ACloakedFly/Thoths-Oracle/Images/20250720_190244.JPG

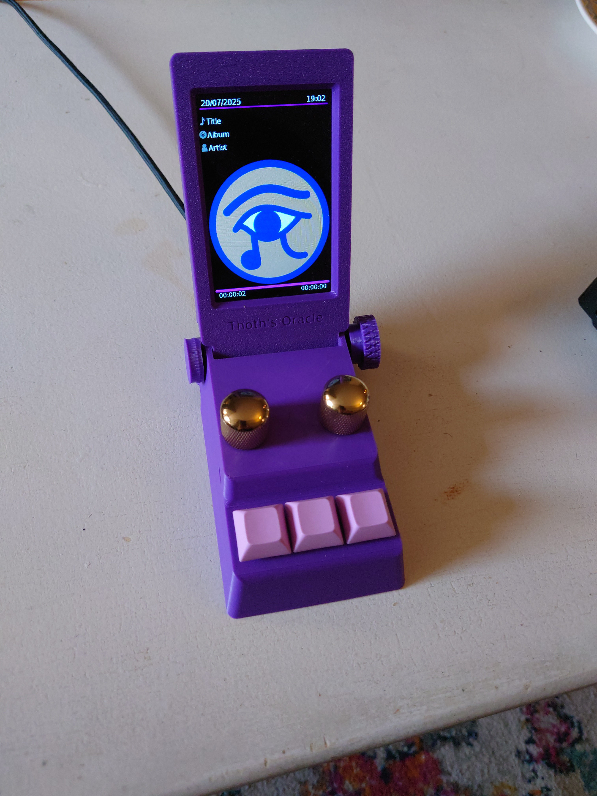
Images/20250720_190244.JPG
