ACloakedFly/Thoths-Oracle/Images/Assembly_Pics/20250726_150619.JPG

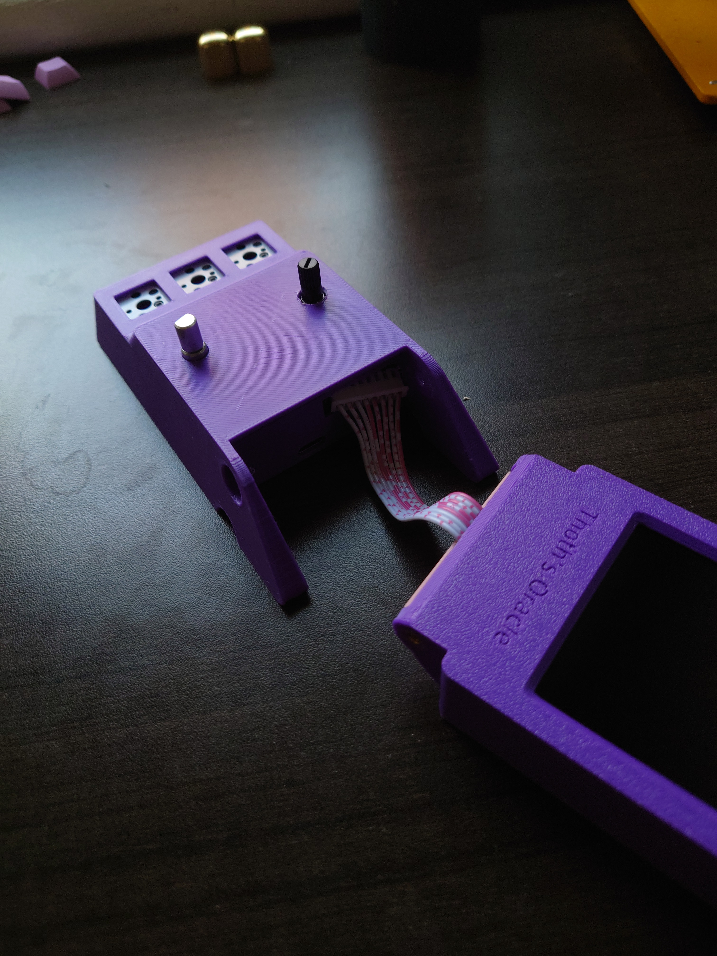
Images/Assembly_Pics/20250726_150619.JPG
