ACloakedFly/Thoths-Oracle/Images/Assembly_Pics/20250726_150648.JPG

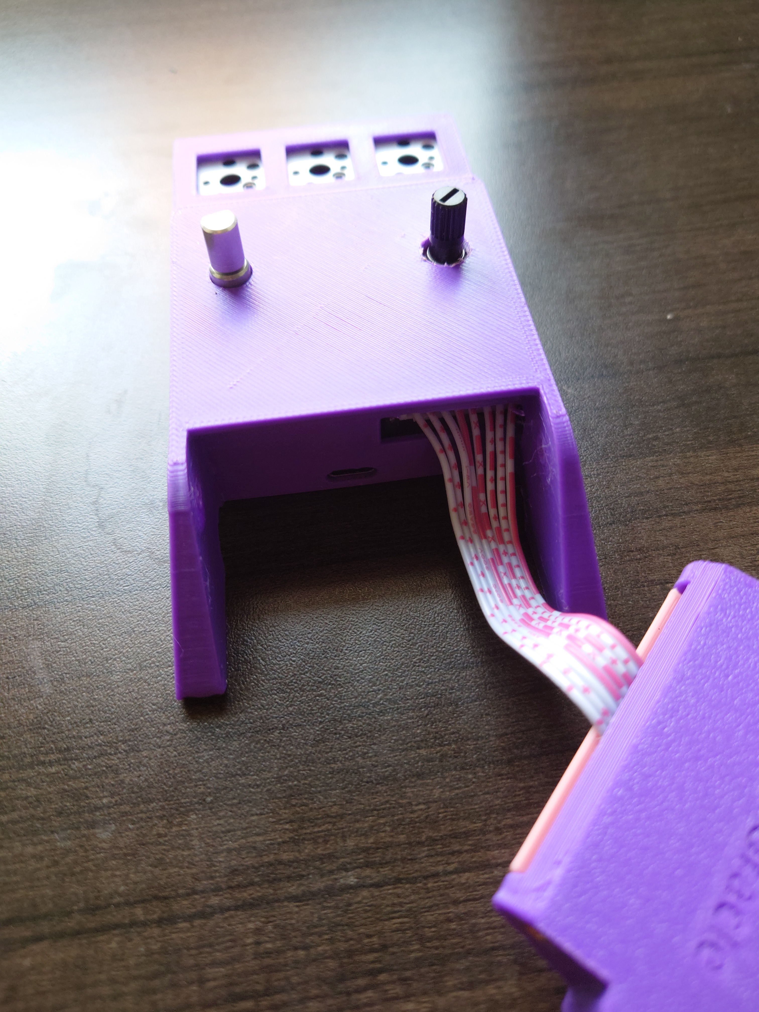
Images/Assembly_Pics/20250726_150648.JPG
