ACloakedFly/Thoths-Oracle/Firmware/main/data.h

/*
===========================================================================
Copyright (C) 2025 Dominique Negm

This file is part of Thoth's Oracle source code.

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
You should have received a copy of the GNU General Public License
along with Thoth's Oracle; if not, see <https://www.gnu.org/licenses/>
===========================================================================
*/
// data.h

#include <string.h>
#include <stdio.h>
#include <stddef.h>
#include <stdlib.h>
#include <stdint.h>
#include <wchar.h>
#include <time.h>
#include "freertos/FreeRTOS.h"
#include "freertos/semphr.h"
#include "freertos/task.h"
#include "freertos/queue.h"
#include "esp_err.h"
#include "esp_log.h"
#include "esp_timer.h"
#include "esp_lcd_panel_io.h"
#include "esp_lcd_panel_vendor.h"
#include "esp_lcd_panel_ops.h"
#include "driver/gpio.h"
#include "driver/spi_master.h"
#include "driver/usb_serial_jtag.h"
#include "driver/ledc.h"
#include "lvgl.h"
#include "button_gpio.h"
#include "iot_button.h"
#include "esp_sleep.h"
#include "driver/pulse_cnt.h"
#include "esp_lcd_ili9341.h"
#include "esp_task_wdt.h"

#define UTF8 1
#define UTF16 2
#define UTF32 4
#define BITS UTF8
#define CHARS 100
#define HEADER_BYTES 12

#define portDelay 50
#define RX_BUF_SIZE (1024)
#define TX_BUF_SIZE (512)

//Inputs
#define PREV_PIN        7
#define MUTE_PIN        2
#define PLAY_PIN        8
#define NEXT_PIN        6
#define ENC_EDGE_PIN    4
#define ENC_LEVEL_PIN   5

//Inputs commands
#define CMD_VAL_VOL_DN      1
#define CMD_VAL_VOL_UP      2
#define CMD_VAL_MUTE        3
#define CMD_VAL_PREV        4
#define CMD_VAL_PLAY_PAUSE  5
#define CMD_VAL_NEXT        6

//Message types
#define IMG_TAG         1
#define TEXT_TAG        2
#define SYS_MSG_TAG     3
#define DUR_POS_TAG     4
#define CMD_TAG         5
#define INFO_TAG        6
#define STATUS_TAG      7
#define FINISHED_TAG    8
#define ERROR_TAG       9
#define COLOUR_TAG      10

//Display
#define PIN_NUM_SCLK        11
#define PIN_NUM_MOSI        10
#define PIN_NUM_LCD_DC      9
#define PIN_NUM_LCD_RST     12
#define PIN_NUM_LCD_CS      13
#define PIN_NUM_MISO        -1//Unused

//Image
#define IMG_WIDTH   304
#define IMG_HEIGHT  304
#define IMG_SIZE IMG_HEIGHT*IMG_WIDTH*2//Images are in RGB565 format so every pixel needs 2 bytes

//Text, added multiple opions to allow for faster testing, can ignore this section
#define TEXT_SIZE 512
#if BITS == 1
#define CHAR_SIZE uint8_t
#define CHAR_TYPE unsigned char
#define char_cpy memcpy
#elif BITS == 2
#define CHAR_SIZE uint16_t
#define CHAR_TYPE wchar_t
#define char_cpy wmemcpy
#else
#define CHAR_SIZE uint32_t
#define CHAR_TYPE wchar_t
#define char_cpy wmemcpy
#endif

#define DUR_POS_BYTES 8
extern const char TAG[3];
extern char name[TEXT_SIZE];
extern bool updated;
extern uint8_t album_cover[IMG_SIZE + RX_BUF_SIZE];//Added an extra buffer at the end just incase
extern uint8_t width, height;
extern uint32_t cover_bytes;
extern uint32_t song_duration;
extern uint32_t song_position;
extern bool name_dirty;
extern bool position_dirty;
extern bool time_dirty;
extern bool theme_dirty;
extern bool img_dirty;
extern bool song_playing;

typedef struct sys_time{
    uint32_t seconds;
    uint8_t date;
    uint8_t month;
    uint16_t year;
} sys_time;
extern sys_time system_time;
extern lv_color32_t system_bar_colour;
extern lv_color32_t system_line_colour;

extern SemaphoreHandle_t info_mutex;
extern SemaphoreHandle_t img_mutex;
extern SemaphoreHandle_t date_time_mutex;

//Icons arrays and image headers for LVGL
extern const uint8_t icon_title[352];
extern const lv_img_dsc_t icon_title_rgb;

extern const uint8_t icon_album[512];
extern const lv_img_dsc_t icon_album_rgb;

extern const uint8_t icon_artist[416];
extern const lv_img_dsc_t icon_artist_rgb;

//LCD
#define LCD_HOST  SPI2_HOST

#define LVGL_TICK_PERIOD_MS    2//Smaller seems better
#define LVGL_HANDLER_PERIOD_MS    20//This effectively determines the framerate LVGL refreshes at, provided the CPU can keep up

#define LCD_PIXEL_CLOCK_HZ     (1000/LVGL_HANDLER_PERIOD_MS)*480*320//This is how fast the SPI connection will communicate. Seems to work best when it is the same as the framerate


// The pixel number in horizontal and vertical
#define LCD_H_RES              320
#define LCD_V_RES              480
#define LCD_BUF 42//Bigger is better, but it seems the ESP32S3 doesn't have enough DMA memory for more than 42

// Bit number used to represent command and parameter bits for SPI connection
#define LCD_CMD_BITS           8
#define LCD_PARAM_BITS         8

//Functions
extern void lvgl_ui(lv_disp_t *disp);
extern void inputs_main();
extern void serial_task(void *pvParameters);
extern void ui_setup(void *pvParameters);
extern void UpdateInfo(void*v);
extern void timer_incer(void *pvParameters);
extern void serial_jtag_write(uint8_t msg_type, char *msg, uint16_t length, TickType_t ticks);
