ACloakedFly/Thoths-Oracle/Firmware/main/lcd_setup.c

/*
===========================================================================
Copyright (C) 2025 Dominique Negm

This file is part of Thoth's Oracle source code.

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
You should have received a copy of the GNU General Public License
along with Thoth's Oracle; if not, see <https://www.gnu.org/licenses/>
===========================================================================
*/
// lcd_setup.c

#include "data.h"
static lv_disp_draw_buf_t disp_buf; // contains internal graphic buffer(s) called draw buffer(s)
static lv_disp_drv_t disp_drv;      // contains callback functions
lv_color_t *buf1;
lv_color_t *buf2;
lv_disp_t *disp;
esp_timer_handle_t lvgl_tick_timer = NULL;
void timer_incer(void* v);

//ESP ILI9341 driver flush callback for LVGL to know when flushing is done
static bool notify_lvgl_flush_ready(esp_lcd_panel_io_handle_t panel_io, esp_lcd_panel_io_event_data_t *edata, void *user_ctx)
{
    lv_disp_drv_t *disp_driver = (lv_disp_drv_t *)user_ctx;
    lv_disp_flush_ready(disp_driver);
    return false;
}

//LVGL callback to do the actual flushing
static void lvgl_flush_cb(lv_disp_drv_t *drv, const lv_area_t *area, lv_color_t *color_map)
{
    esp_lcd_panel_handle_t panel_handle = (esp_lcd_panel_handle_t) drv->user_data;
    int offsetx1 = area->x1;
    int offsetx2 = area->x2;
    int offsety1 = area->y1;
    int offsety2 = area->y2;
    // copy a buffer's content to a specific area of the display
    esp_lcd_panel_draw_bitmap(panel_handle, offsetx1, offsety1, offsetx2 + 1, offsety2 + 1, color_map);
}

//An ESP timer is registered to handle LVGL tick incrementing
static void increase_lvgl_tick()
{
    /* Tell LVGL how many milliseconds has elapsed */
    lv_tick_inc(LVGL_TICK_PERIOD_MS);
}
//A task is created with a higher priority than main LVGL task to handle timer registration
void timer_incer(void* v){
    const esp_timer_create_args_t lvgl_tick_timer_args = {
        .callback = &increase_lvgl_tick,
        .name = "lvgl_tick"
    };
    ESP_LOGI(TAG, "Install LVGL tick timer");

    ESP_ERROR_CHECK(esp_timer_create(&lvgl_tick_timer_args, &lvgl_tick_timer));
    ESP_ERROR_CHECK(esp_timer_start_periodic(lvgl_tick_timer, LVGL_TICK_PERIOD_MS * 1000));  
    vTaskDelete(NULL);
}

void ui_setup(void *pvParameters){

    ESP_LOGI(TAG, "Initialize SPI bus");
    spi_bus_config_t buscfg = {
        .sclk_io_num = PIN_NUM_SCLK,
        .mosi_io_num = PIN_NUM_MOSI,
        .miso_io_num = PIN_NUM_MISO,
        .quadwp_io_num = -1,
        .quadhd_io_num = -1,
        .max_transfer_sz = LCD_H_RES * LCD_BUF * sizeof(lv_color_t),
    };
    ESP_ERROR_CHECK(spi_bus_initialize(LCD_HOST, &buscfg, SPI_DMA_CH_AUTO));

    ESP_LOGI(TAG, "Install panel IO");
    esp_lcd_panel_io_handle_t io_handle = NULL;
    esp_lcd_panel_io_spi_config_t io_config = {
        .dc_gpio_num = PIN_NUM_LCD_DC,
        .cs_gpio_num = PIN_NUM_LCD_CS,
        .pclk_hz = LCD_PIXEL_CLOCK_HZ,
        .lcd_cmd_bits = LCD_CMD_BITS,
        .lcd_param_bits = LCD_PARAM_BITS,
        .spi_mode = 0,
        .trans_queue_depth = 10,
        .on_color_trans_done = notify_lvgl_flush_ready,
        .user_ctx = &disp_drv,
    };
    // Attach the LCD to the SPI bus
    ESP_ERROR_CHECK(esp_lcd_new_panel_io_spi((esp_lcd_spi_bus_handle_t)LCD_HOST, &io_config, &io_handle));

    esp_lcd_panel_handle_t panel_handle = NULL;
    esp_lcd_panel_dev_config_t panel_config = {
        .reset_gpio_num = PIN_NUM_LCD_RST,
        .rgb_endian = LCD_RGB_ENDIAN_BGR,
        .bits_per_pixel = 16,
    };

    ESP_LOGI(TAG, "Install ILI9341 panel driver");
    ESP_ERROR_CHECK(esp_lcd_new_panel_ili9341(io_handle, &panel_config, &panel_handle));
    ESP_LOGI(TAG, "Panel driver installed");

    ESP_ERROR_CHECK(esp_lcd_panel_reset(panel_handle));
    ESP_ERROR_CHECK(esp_lcd_panel_init(panel_handle));
    ESP_ERROR_CHECK(esp_lcd_panel_invert_color(panel_handle, true));
    ESP_LOGI(TAG, "Panel init");

    ESP_ERROR_CHECK(esp_lcd_panel_mirror(panel_handle, true, false));
    ESP_LOGI(TAG, "Panel Mirror");

    // user can flush pre-defined pattern to the screen before we turn on the screen or backlight
    ESP_ERROR_CHECK(esp_lcd_panel_disp_on_off(panel_handle, true));
    ESP_LOGI(TAG, "Panel Disp_on_off");

    ESP_LOGI(TAG, "Initialize LVGL library");
    lv_init();
    // alloc draw buffers used by LVGL
    // it's recommended to choose the size of the draw buffer(s) to be at least 1/10 screen sized
    buf1 = heap_caps_malloc(LCD_H_RES * LCD_BUF * sizeof(lv_color_t), MALLOC_CAP_DEFAULT);
    assert(buf1);
    buf2 = heap_caps_malloc(LCD_H_RES * LCD_BUF * sizeof(lv_color_t), MALLOC_CAP_DMA);
    assert(buf2);
    
    // initialize LVGL draw buffers
    lv_disp_draw_buf_init(&disp_buf, buf1, buf2, LCD_H_RES * LCD_BUF);

    ESP_LOGI(TAG, "Register display driver to LVGL");
    lv_disp_drv_init(&disp_drv);
    disp_drv.hor_res = LCD_H_RES;
    disp_drv.ver_res = LCD_V_RES;
    disp_drv.flush_cb = lvgl_flush_cb;
    disp_drv.draw_buf = &disp_buf;
    disp_drv.user_data = panel_handle;
    disp_drv.full_refresh = 0;
    disp_drv.screen_transp = 0;
    disp_drv.antialiasing = 0;
    disp_drv.direct_mode = 0;
    disp_drv.sw_rotate = 0;
    disp = lv_disp_drv_register(&disp_drv);
    
    lvgl_ui(disp);
}
