ACloakedFly/Thoths-Oracle/Images/Assembly_Pics/20250726_151238.JPG

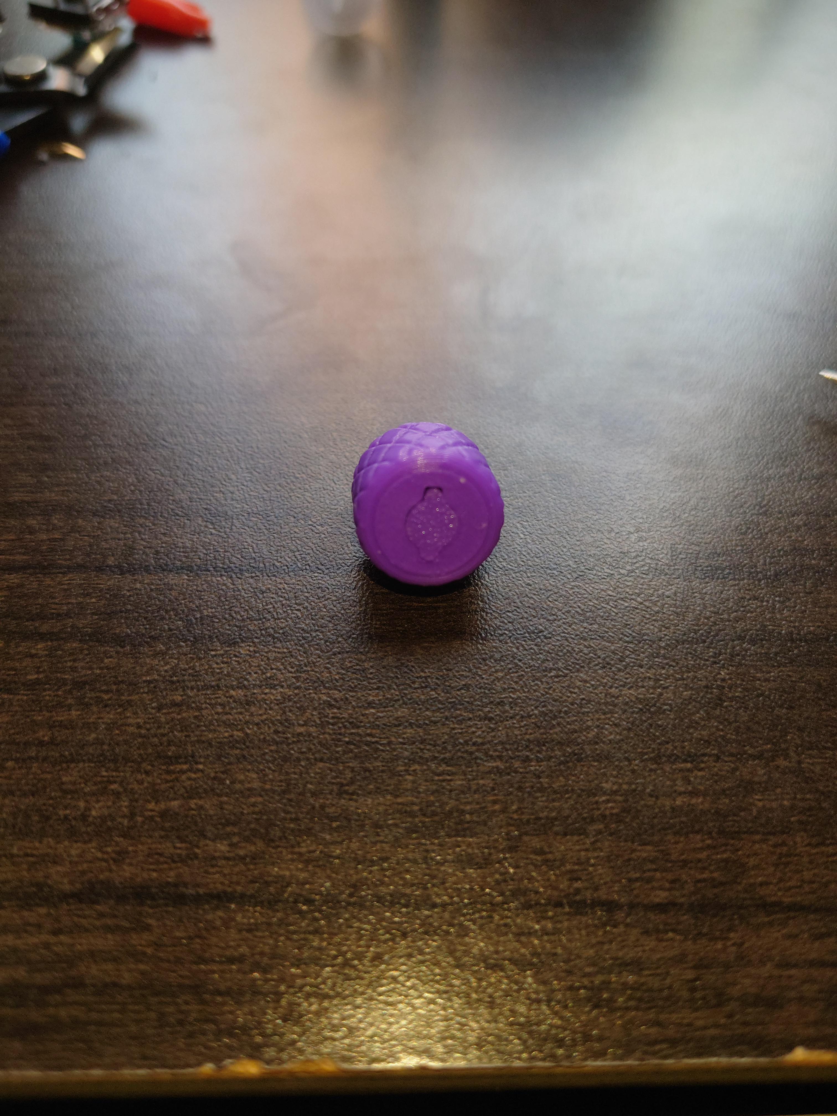
Images/Assembly_Pics/20250726_151238.JPG
