ACloakedFly/Thoths-Oracle/Images/Assembly_Pics/20250727_092545.JPG

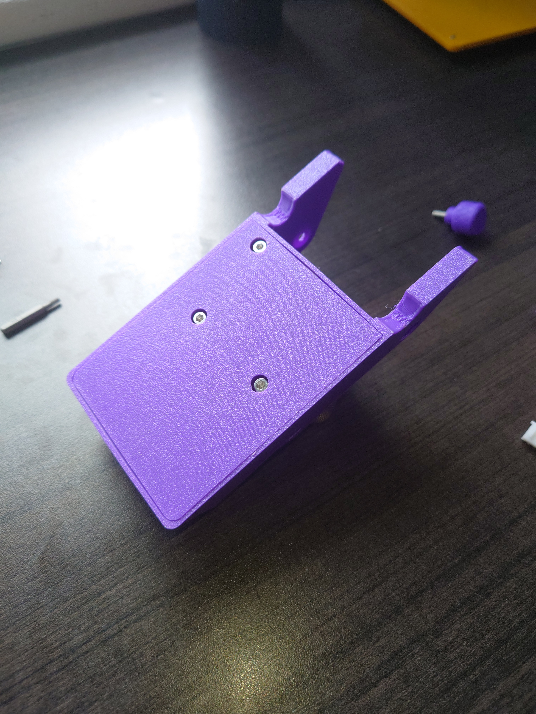
[picture p22: Images/Assembly_Pics/20250727_092545.JPG]
Images/Assembly_Pics/20250727_092545.JPG
